piotr-kubica/ir-pc-volume-control-knob/mycust_font.h

/*
  Fontname: cust
  Copyright: unknown
  Glyphs: 3/3
  BBX Build Mode: 0
*/
const uint8_t mycust_font[125] U8G2_FONT_SECTION("mycust_font") = 
  "\3\0\4\4\5\5\5\4\7\35\20\2\5\25\0\25\0\0\0\0\0\0`A)\32\326\6\203X\261C"
  "\207\26,x\354\30*Tj\324,Y\362\340\7C\226\250Q\203\12\325\261c\5\13\222\34*V,\0"
  "B\31\17\346\6\203\330\222\350\222\255b\323\342\301\3\27M\26\251Bg\262\254\0C\34\32\312\6\257\244"
  "#\11Vv\25\66\232,y\360\203!\333h\205\331\205UR+\1\0\0\0\4\377\377\0";
